NXP-MCU-X-Lab/dm-mcxa-encoder/source/mcux_config.h

/*
 * Copyright 2025 NXP
 *
 * SPDX-License-Identifier: BSD-3-Clause
 */

#ifndef _MCUX_CONFIG_H_
#define _MCUX_CONFIG_H_

#define CONFIG_FLASH_BASE_ADDRESS 0x0


#define APP_MODE_FREEMASTER       5

#endif /* _MCUX_CONFIG_H_ */
